bablokb/christmas-box/build/hinges.jpg

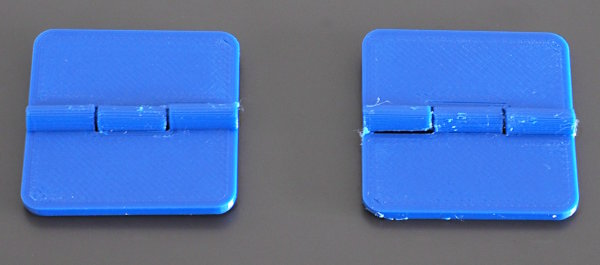
build/hinges.jpg
