bablokb/christmas-box/build/inner-plate.jpg

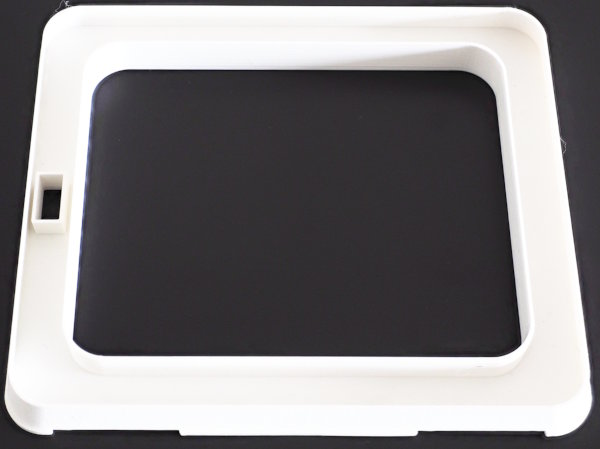
build/inner-plate.jpg
