bablokb/christmas-box/build/outer-shell+inner-shell+inner-plate.jpg

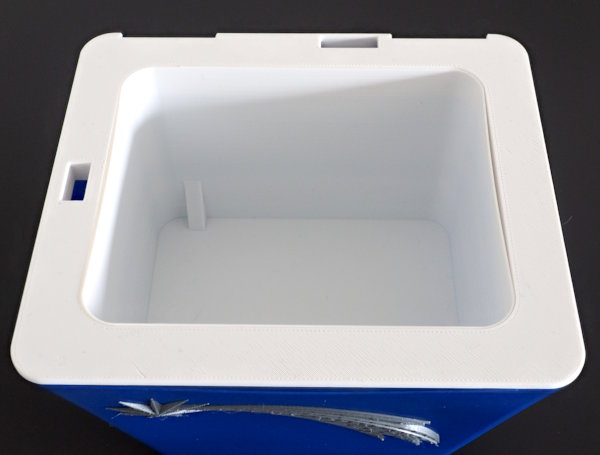
build/outer-shell+inner-shell+inner-plate.jpg
